oresat/low-gain-radio/firmware/common/include/v1_2.h

/*! \file v1_2.h
 */

/* Board specific defines in this file */

#ifndef _V1_2_H_
#define _V1_2_H_

extern const char _lgr_version[10];

#define UART_INPUT_CLOCKSPEED                       24000000U
#define TPM_INPUT_CLOCKSPEED                       	24000000U

/* CMSIS For this revision */
#define         __CM0PLUS_REV                       0x0000U

#define         __MPU_PRESENT                       0U

#define         __VTOR_PRESENT                      0U

#define         __NVIC_PRIO_BITS                    2U

#define         __Vendor_SysTickConfig              0U

#endif
