oresat/low-gain-radio/firmware/drivers/include/doxy.h

/*!
   \mainpage ORESAT - PSAS Low Gain Radio Project Firmware
   *
   * Introduction
   * ------------
   *
  
   This firmware is targeted for the Low Gain Radio (LGR) boards based on the NXP MKW01Z128 Arm Cortex M0plus based wireless single package device.

   <a href="http://www.nxp.com/products/interface-and-connectivity/wireless-connectivity/sub-1-ghz-wireless-solutions/kinetis-kw0x-48-mhz-sub-1-ghz-wireless-radio-microcontrolle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">MKW01Z128 Vendor Information</a>

   *
   */
